stgloorious/current-probe/sim/notch_filter.asc

C1: cap; 1µ
C2: cap; 330n
C3: cap; 10µ
C4: cap; 47n
L1: ind; 6.8µ; Ipk=0.55 Rser=0.25
L2: ind; 100µ; Rser=3.5
L3: ind; 100µ; Rser=3.5
R1: res; 100
R2: res; 100m
V1: voltage; ""; AC 1
Named nets: OUT, 0, IN
.ac dec 1000 10 1e9
DC/DC converter
To linear regulator
